regamp/I2C-extender/Pictures/I2C_relay_module5.png

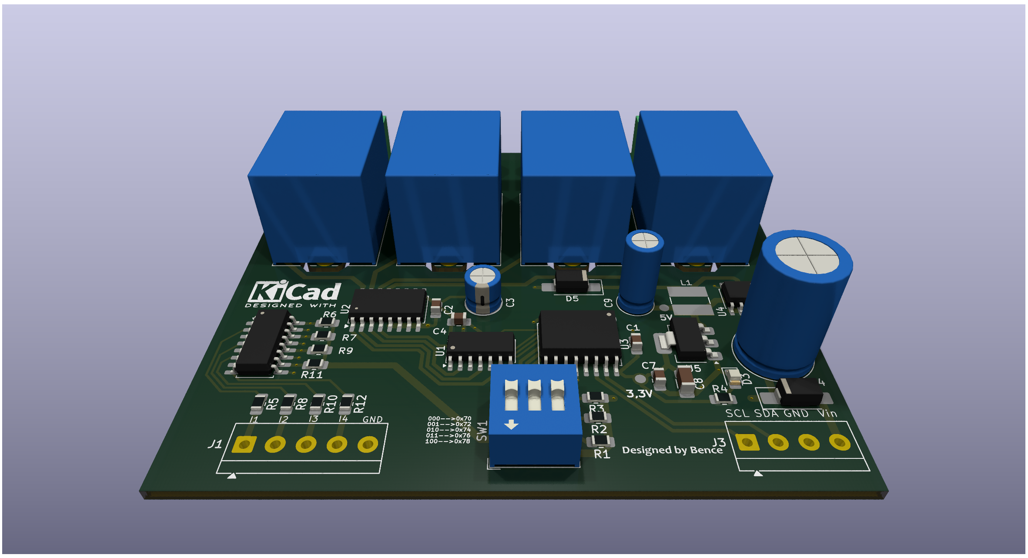
Pictures/I2C_relay_module5.png
