regamp/I2C-extender/Pictures/I2C_relay_module6.png

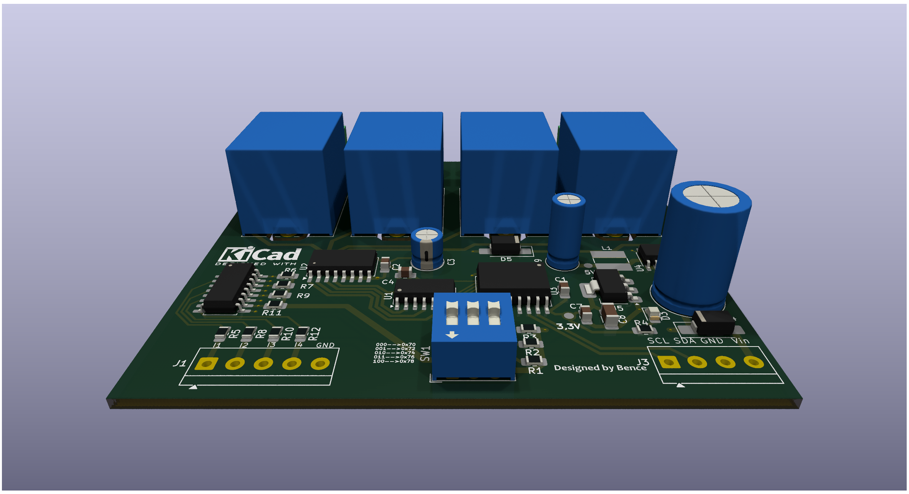
Pictures/I2C_relay_module6.png
