regamp/I2C-extender/Pictures/I2C_relay_module13.png

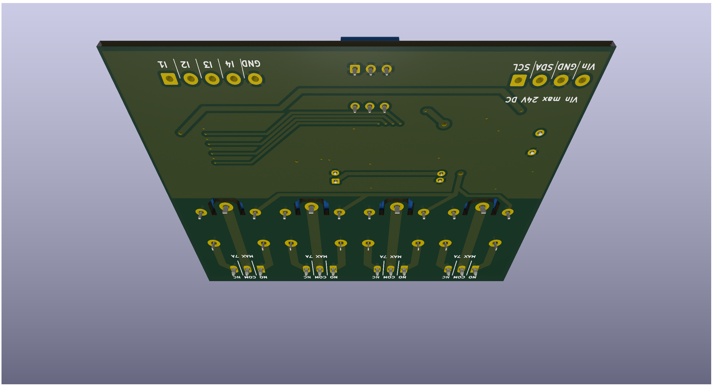
Pictures/I2C_relay_module13.png
