regamp/I2C-extender/Pictures/I2C_relay_module14.png

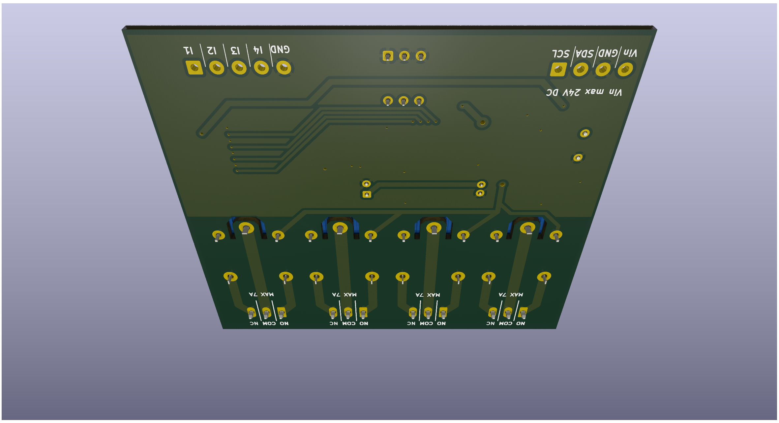
Pictures/I2C_relay_module14.png
